hayden-t/arduino-door-monitor/doors_base/doors.h

typedef struct {
  char name[4];
  boolean alarm;
  unsigned long stamp;
} door;

const int maxDoors = 39;

door doors[maxDoors] = {
  {"082"},//0
  {"083"},
  {"084"},
  {"085"},
  {"086"},
  {"087"},
  {"088"},
  {"089"},
  {"090"},
  {"091"},
  {"092"},//10
  {"093"},
  {"094"},
  {"095"},
  {"096"},
  {"097"},
  {"098"},
  {"099"},
  {"100"},
  {"101"},
  {"102"},//20
  {"103"},
  {"104"},
  {"105"},
  {"106"},
  {"107"},
  {"108"},
  {"109"},
  {"110"},
  {"111"},
  {"112"},//30
  {"113"},
  {"114"},
  {"115"},
  {"116"},
  {"QRM"},//35
  {"SR1"},//36
  {"SR2"},//37
  {"LIN"}//38
};
