hayden-t/arduino-door-monitor/doors_mobile/graphics.h

#include <avr/pgmspace.h>


uint8_t tower[] PROGMEM={
0x01, 0x03, 0x05, 0x7F, 0x05, 0x03, 0x01, 
};

uint8_t loading[] PROGMEM={
0x40, 0x00, 0x40, 0x00, 0x40, 0x00, 0x00, 0x00, 0x41, 0x77, 0x5D, 0x77, 0x41, 0x00, 
};

uint8_t signal1[] PROGMEM={
0x40, 0x00, 0x00, 0x00, 0x00, 0x00, 0x00, 0x00, 0x00, 0x00, 0x00, 0x00, 0x00, 0x00, 
};
uint8_t signal2[] PROGMEM={
0x40, 0x00, 0x60, 0x00, 0x00, 0x00, 0x00, 0x00, 0x00, 0x00, 0x00, 0x00, 0x00, 0x00,
};
uint8_t signal3[] PROGMEM={
0x40, 0x00, 0x60, 0x00, 0x70, 0x00, 0x00, 0x00, 0x00, 0x00, 0x00, 0x00, 0x00, 0x00,
};
uint8_t signal4[] PROGMEM={
0x40, 0x00, 0x60, 0x00, 0x70, 0x00, 0x78, 0x00, 0x00, 0x00, 0x00, 0x00, 0x00, 0x00,
};
uint8_t signal5[] PROGMEM={
0x40, 0x00, 0x60, 0x00, 0x70, 0x00, 0x78, 0x00, 0x7C, 0x00, 0x00, 0x00, 0x00, 0x00, 
};
uint8_t signal6[] PROGMEM={
0x40, 0x00, 0x60, 0x00, 0x70, 0x00, 0x78, 0x00, 0x7C, 0x00, 0x7E, 0x00, 0x00, 0x00, 
};
uint8_t signal7[] PROGMEM={
0x40, 0x00, 0x60, 0x00, 0x70, 0x00, 0x78, 0x00, 0x7C, 0x00, 0x7E, 0x00, 0x7F, 0x00, 
};

uint8_t battery0[] PROGMEM={
0x00, 0x1C, 0x7F, 0x41, 0x41, 0x41, 0x41, 0x41, 0x41, 0x41, 0x41, 0x41, 0x7F, 0x00, 
};
uint8_t battery1[] PROGMEM={
0x00, 0x1C, 0x7F, 0x41, 0x41, 0x41, 0x41, 0x41, 0x41, 0x41, 0x41, 0x7F, 0x7F, 0x00, 
};
uint8_t battery2[] PROGMEM={
0x00, 0x1C, 0x7F, 0x41, 0x41, 0x41, 0x41, 0x41, 0x41, 0x41, 0x7F, 0x7F, 0x7F, 0x00, 
};
uint8_t battery3[] PROGMEM={
0x00, 0x1C, 0x7F, 0x41, 0x41, 0x41, 0x41, 0x41, 0x41, 0x7F, 0x7F, 0x7F, 0x7F, 0x00, 
};
uint8_t battery4[] PROGMEM={
0x00, 0x1C, 0x7F, 0x41, 0x41, 0x41, 0x41, 0x41, 0x7F, 0x7F, 0x7F, 0x7F, 0x7F, 0x00, 
};
uint8_t battery5[] PROGMEM={
0x00, 0x1C, 0x7F, 0x41, 0x41, 0x41, 0x41, 0x7F, 0x7F, 0x7F, 0x7F, 0x7F, 0x7F, 0x00, 
};
uint8_t battery6[] PROGMEM={
0x00, 0x1C, 0x7F, 0x41, 0x41, 0x41, 0x7F, 0x7F, 0x7F, 0x7F, 0x7F, 0x7F, 0x7F, 0x00, 
};
uint8_t battery7[] PROGMEM={
0x00, 0x1C, 0x7F, 0x41, 0x41, 0x7F, 0x7F, 0x7F, 0x7F, 0x7F, 0x7F, 0x7F, 0x7F, 0x00, 
};
uint8_t battery8[] PROGMEM={
0x00, 0x1C, 0x7F, 0x41, 0x7F, 0x7F, 0x7F, 0x7F, 0x7F, 0x7F, 0x7F, 0x7F, 0x7F, 0x00, 
};
uint8_t battery9[] PROGMEM={
0x00, 0x1C, 0x7F, 0x7F, 0x7F, 0x7F, 0x7F, 0x7F, 0x7F, 0x7F, 0x7F, 0x7F, 0x7F, 0x00, 
};
