hayden-t/arduino-door-monitor/wifi_board/code/TEST_MEGA-ESP/TEST_MEGA-ESP.ino

#include "MemoryFree.h"
#include <EEPROM.h>

#define PIN_LED 13
String inString;

void setup() {
  Serial.begin(115200);
  Serial3.begin(115200);
  pinMode(PIN_LED, OUTPUT);
  digitalWrite(PIN_LED, LOW);
}

void loop() {
  serialEvent3();
}

void serialEvent3() {
  while (Serial3.available()) {
    char inChar = Serial3.read();
    Serial.write(inChar);
    inString += inChar;
    if (inChar == ']') {
      if (inString.indexOf("[ON]")>0) {
        digitalWrite(PIN_LED, HIGH);
      }
      else if (inString.indexOf("[OFF]")>0) {
        digitalWrite(PIN_LED, LOW);
      }
      else
      {
        Serial.println("Wrong command");
      }
      inString = "";
    }
  }
}
